AvishkaVishwa/ESP32_C3_with_MAX7219_Diaplay_Driver/assest/2.png

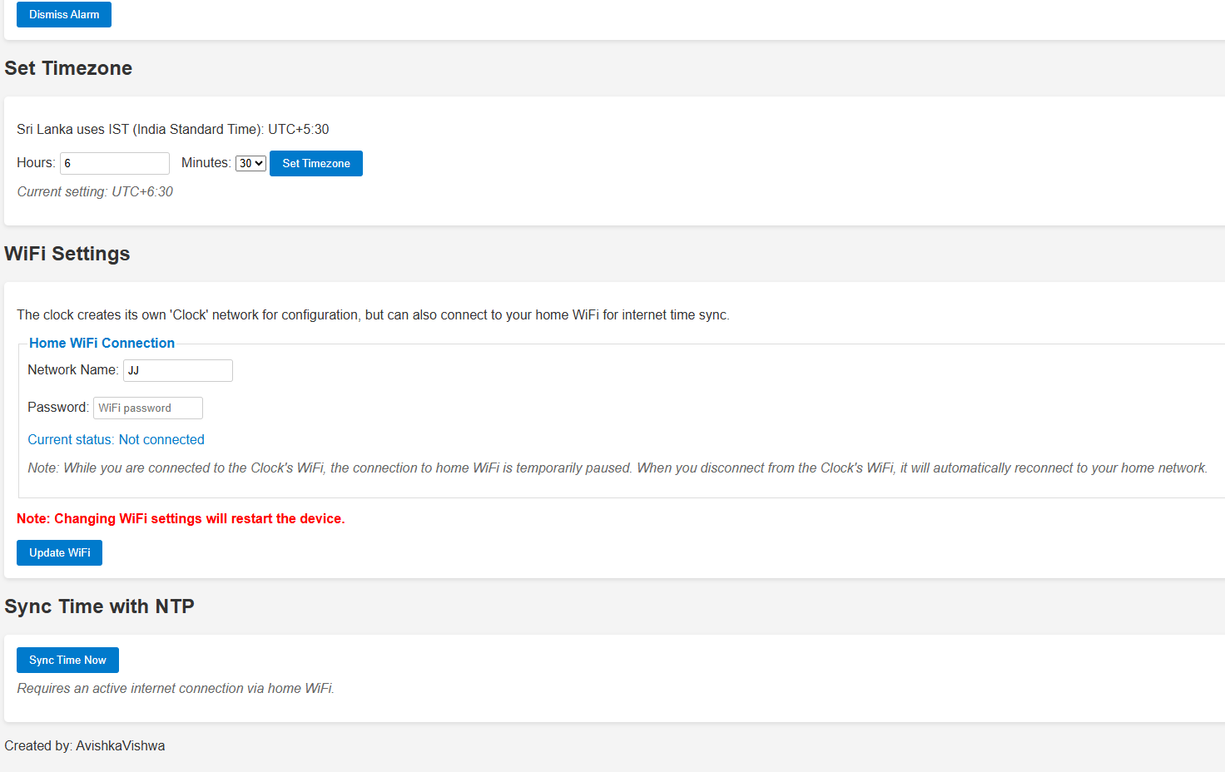
assest/2.png
