AvishkaVishwa/ESP32_C3_with_MAX7219_Diaplay_Driver/assest/pcbWAY.png

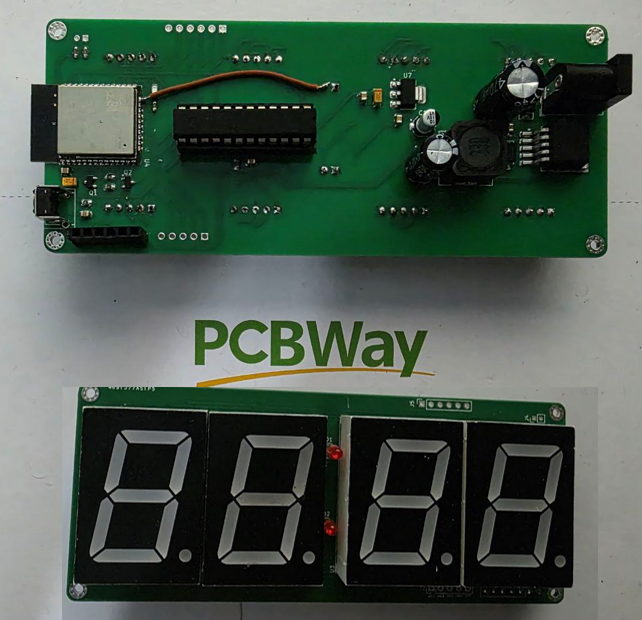
assest/pcbWAY.png
