AvishkaVishwa/ESP32_C3_with_MAX7219_Diaplay_Driver/assest/web_interface.png

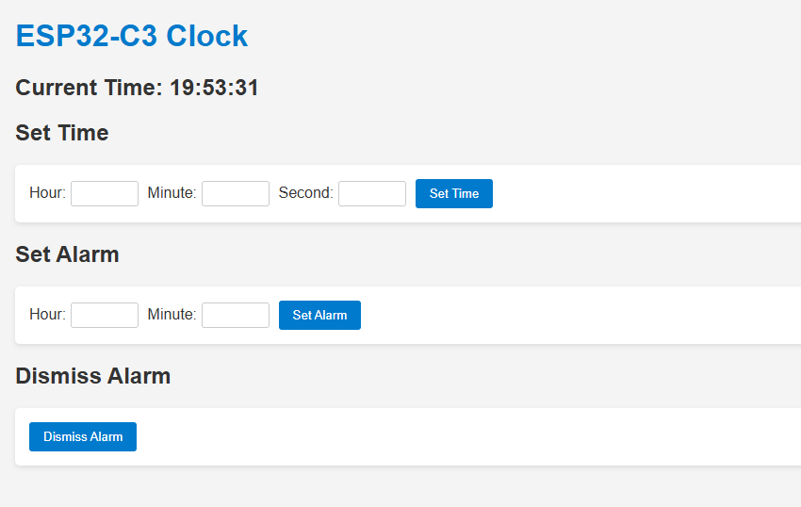
assest/web_interface.png
